ci-rt/testbox-shield/docs/r12.jpg

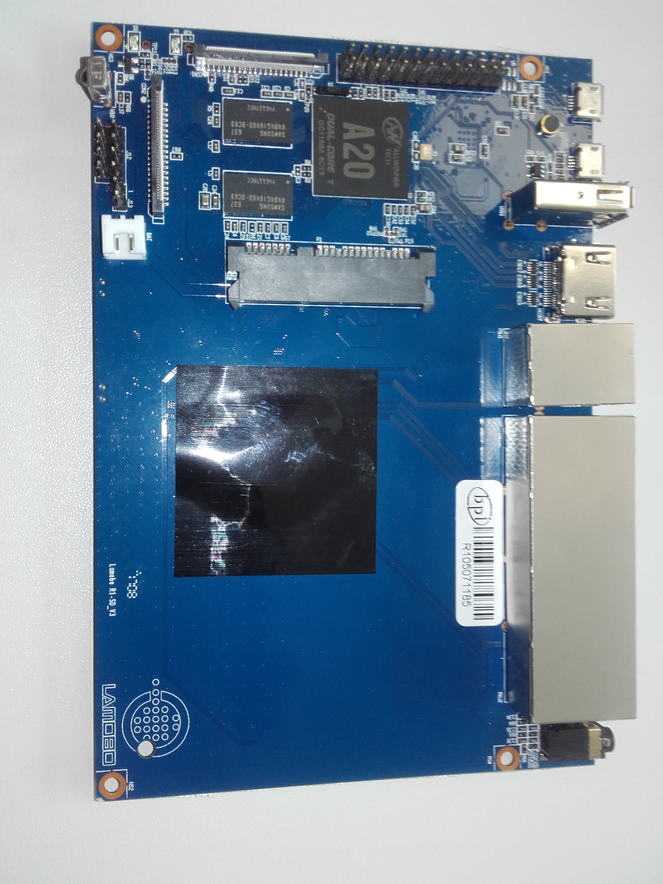
docs/r12.jpg
