ci-rt/testbox-shield/docs/Rocker_8600_8650_series-DTE.pdf

# 8600 Rocker Switches - Miniature

# 10A 250Vac Single & Double Pole

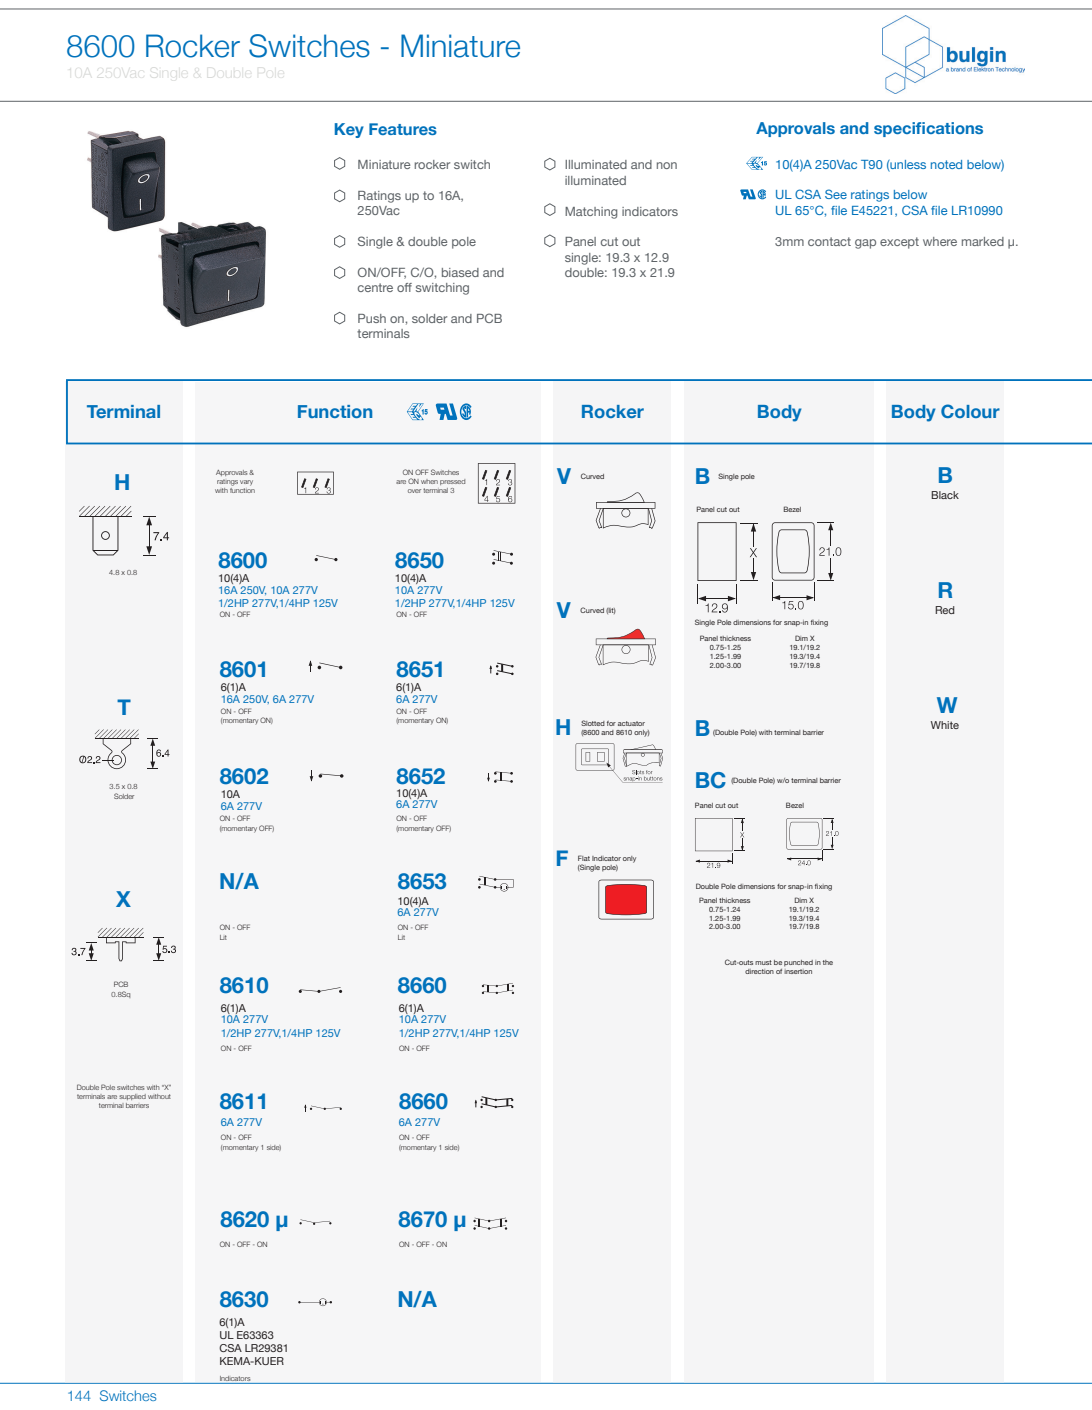
[picture p69: page 1]
144 Switches; Terminal; Function; 3.5 x 0.8 Solder; PCB 0.8Sq; Rocker; Body; Body Colour; V Curved; V Curved (lit); Indicators; 6(1)A UL E63363 CSA LR29381 KEMA-KUER; ON - OFF; (momentary ON); (momentary OFF); ON - OFF Lit; ON - OFF (momentary 1 side); ON - OFF - ON; Single pole; Panel cut out; Bezel; Dim X 19.1/19.2 19.3/19.4 19.7/19.8; Approvals & ratings vary with function; ON OFF Switches are ON when pressed over terminal 3; Key Features; Black; White; Red

Approvals and specifications

Miniature rocker switch
Ratings up to 16A,
250Vac
Single & double pole
ON/OFF, C/O, biased and
centre off switching
Push on, solder and PCB
terminals

Illuminated and non
illuminated
Matching indicators
Panel cut out
single: 19.3 x 12.9
double: 19.3 x 21.9

10(4)A 250Vac T90 (unless noted below)
UL CSA See ratings below
UL 65°C, file E45221, CSA file LR10990
3mm contact gap except where marked μ.

Single Pole dimensions for snap-in fixing
Panel thickness

Slotted for actuator H (8600 and 8610 only)

B(Double Pole) with terminal barrier

(Double Pole) w/o terminal barrier

Flat Indicator only F (Single pole)

Double Pole dimensions for snap-in fixing

Cut-outs must be punched in the
direction of insertion

Double Pole switches with “X”
terminals are supplied without
terminal barriers

# Dimensions

Single pole | Double pole

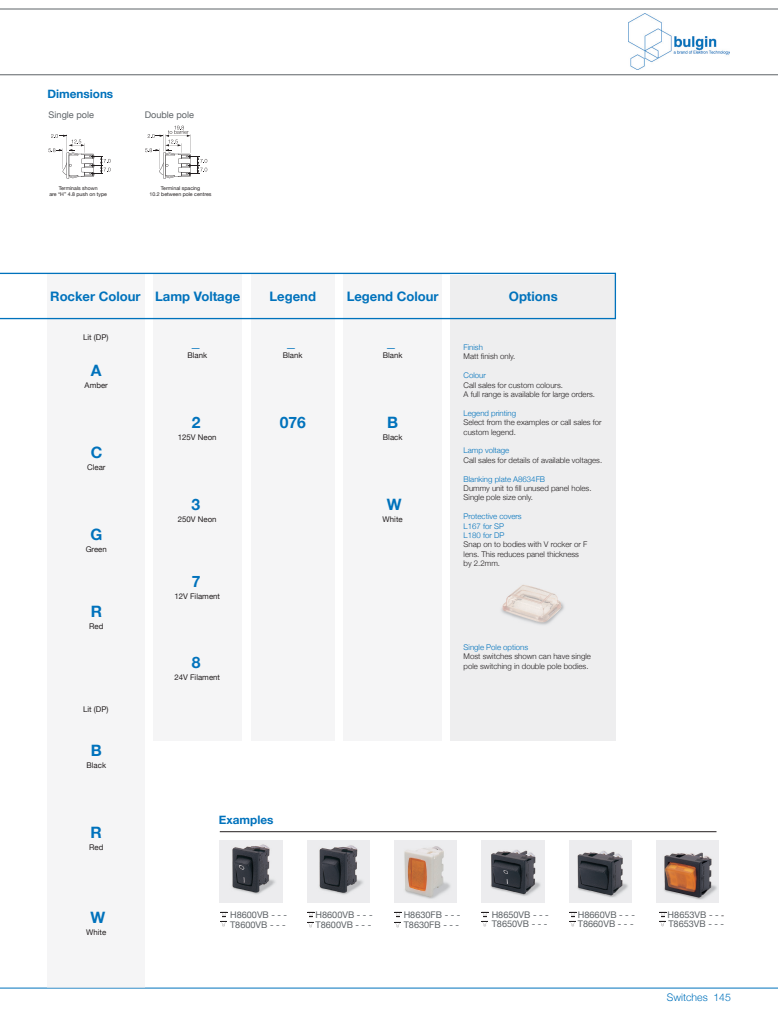
[picture p70: page 2]
Switches 145; Examples; Blank; Amber; Red; 12V Filament; 24V Filament; White; Green; 250V Neon; Black; Clear; 125V Neon; Lit (DP)

Terminals shown
are “H” 4.8 push on type

Terminal spacing
10.2 between pole centres

Rocker Colour | Lamp Voltage | Legend | Legend Colour | Options

Finish Matt finish only. Colour Call sales for custom colours. A full range is available for large orders. Legend printing Select from the examples or call sales for custom legend. Lamp voltage Call sales for details of available voltages. Blanking plate A8634FB Dummy unit to fill unused panel holes. Single pole size only. Protective covers L167 for SP L180 for DP Snap on to bodies with V rocker or F lens. This reduces panel thickness

Single Pole options
Most switches shown can have single
pole switching in double pole bodies.
