ci-rt/testbox-shield/docs/IRM-20-EN.pdf

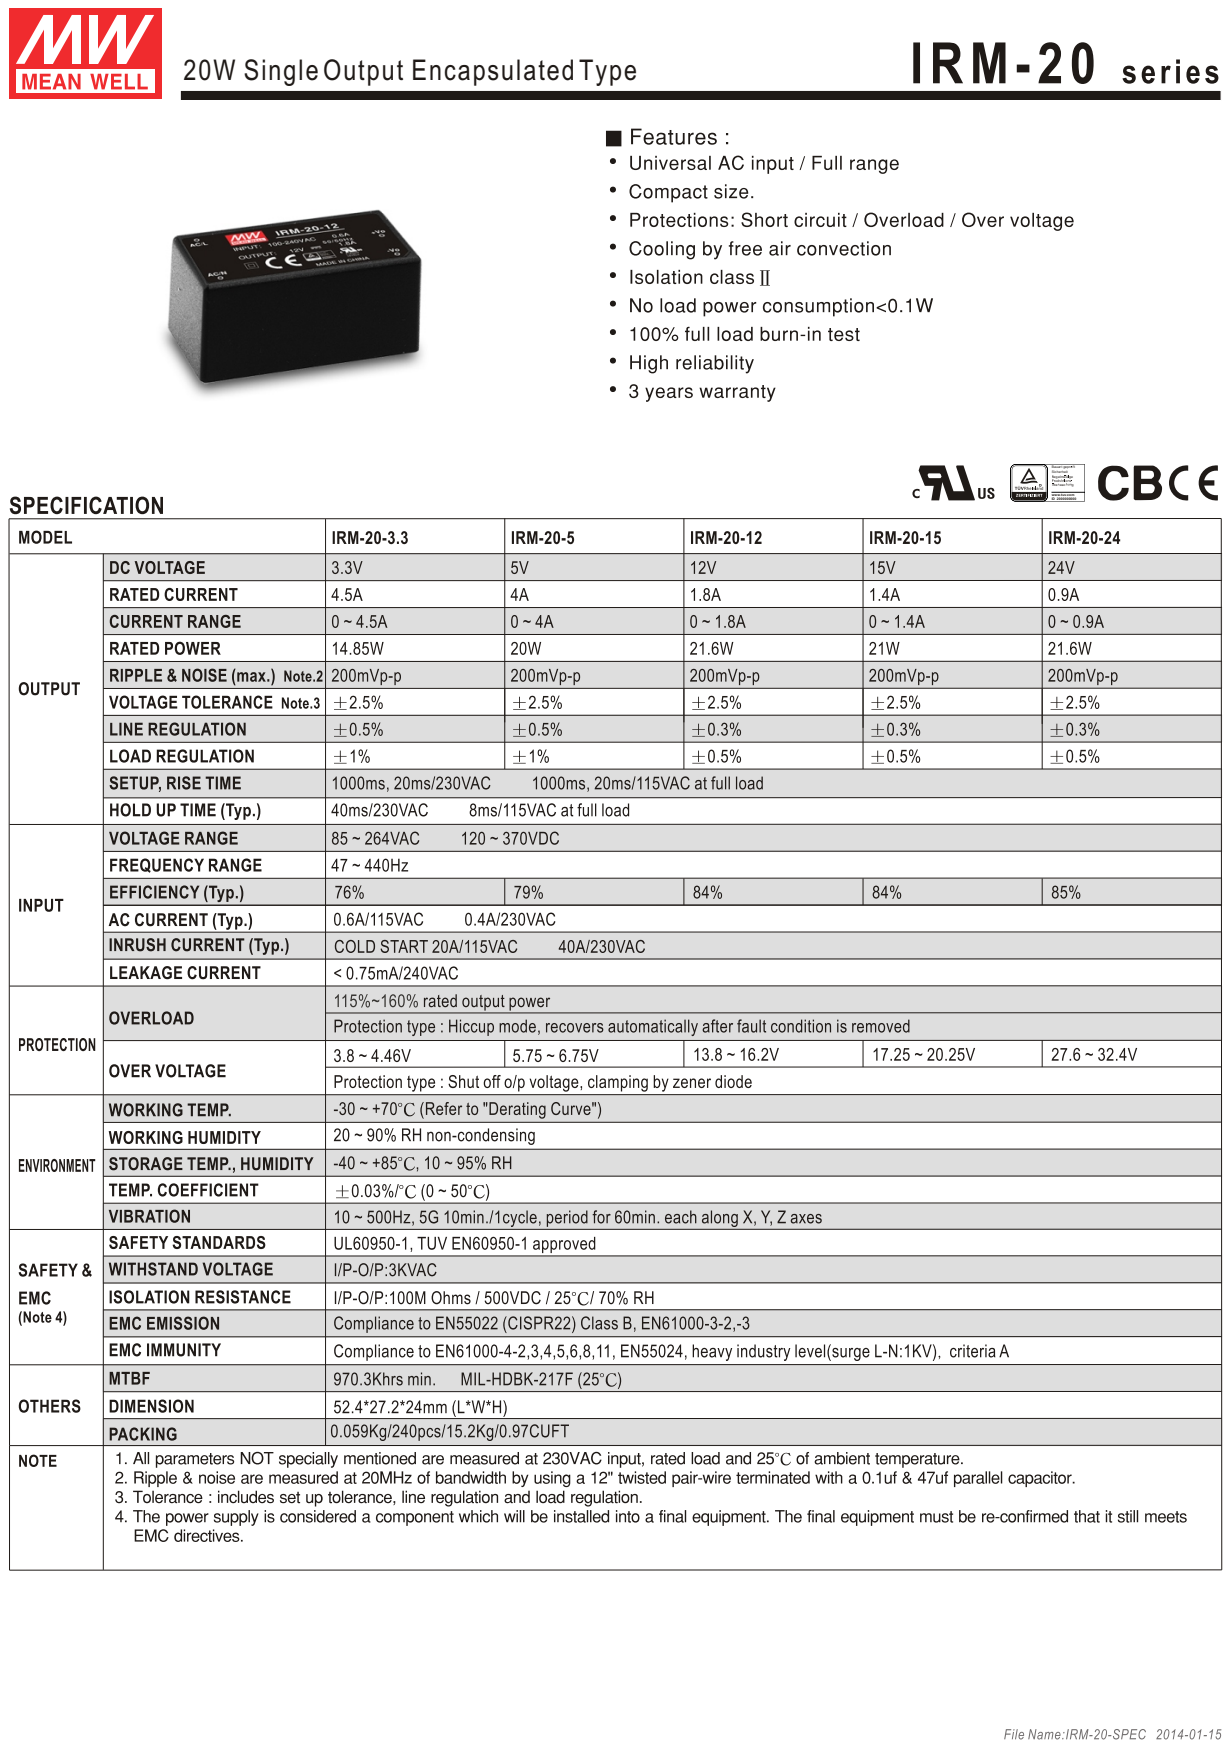
[picture p71: page 1]
Bauar Sicherheit egelma ge; t gepruft; www. ID 2000000000; tuv.com; wac

20W Single Output Encapsulated Type

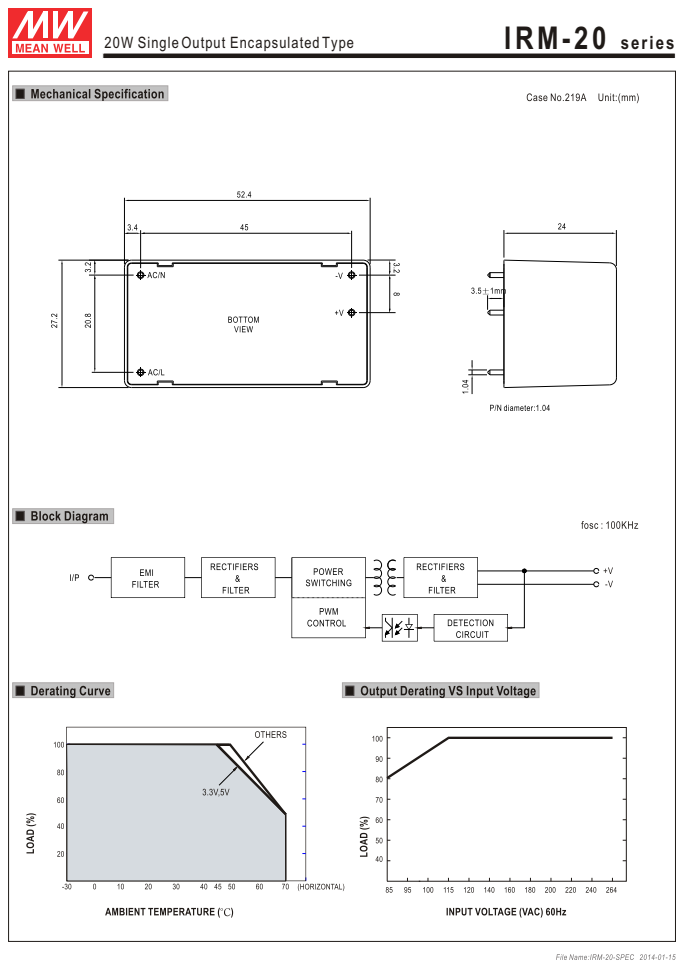
[picture p72: page 2]
20W Single Output Encapsulated Type; IRM-20 series
