ci-rt/testbox-shield/docs/TME-IEC-C-X.pdf

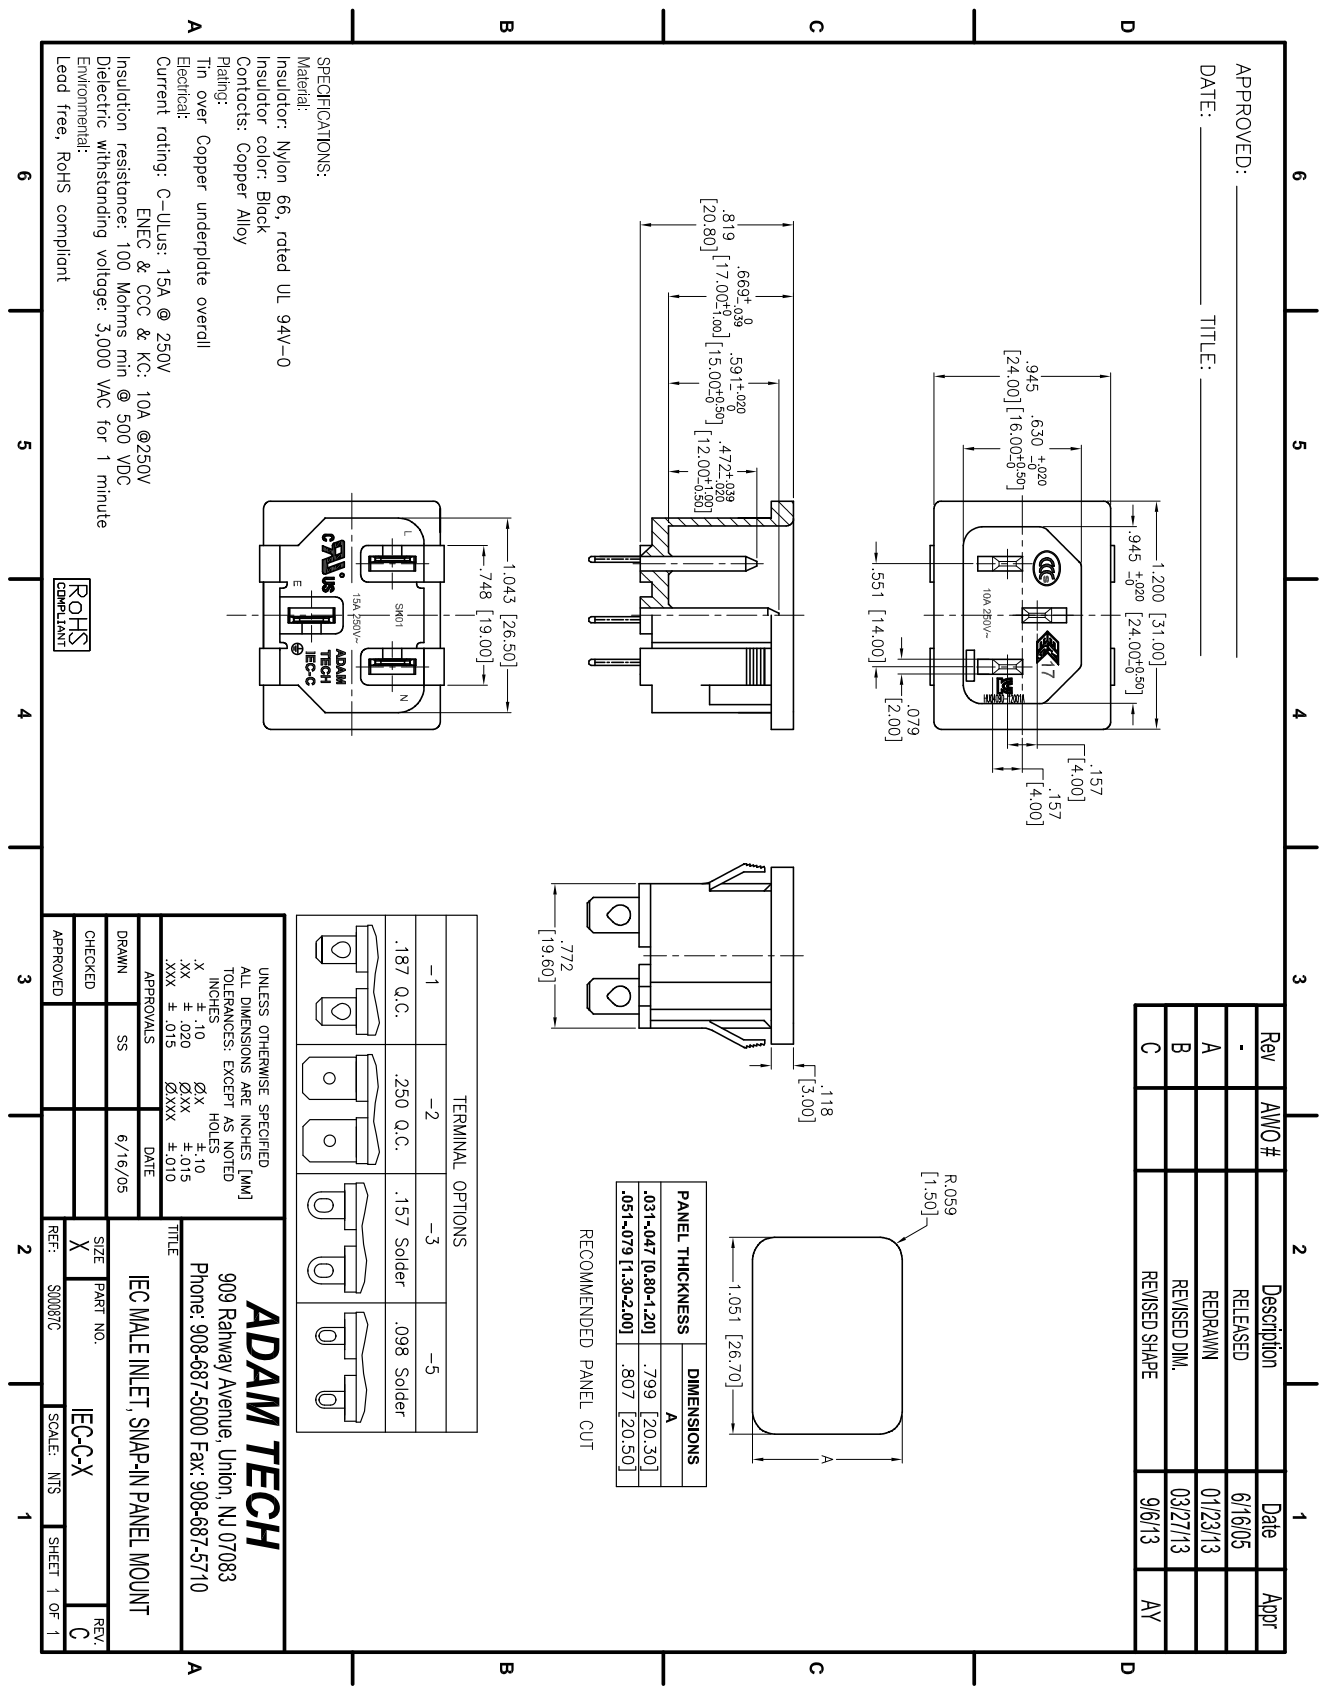
[picture p73: page 1]
