ci-rt/testbox-shield/docs/TME-IEC-D-X.pdf

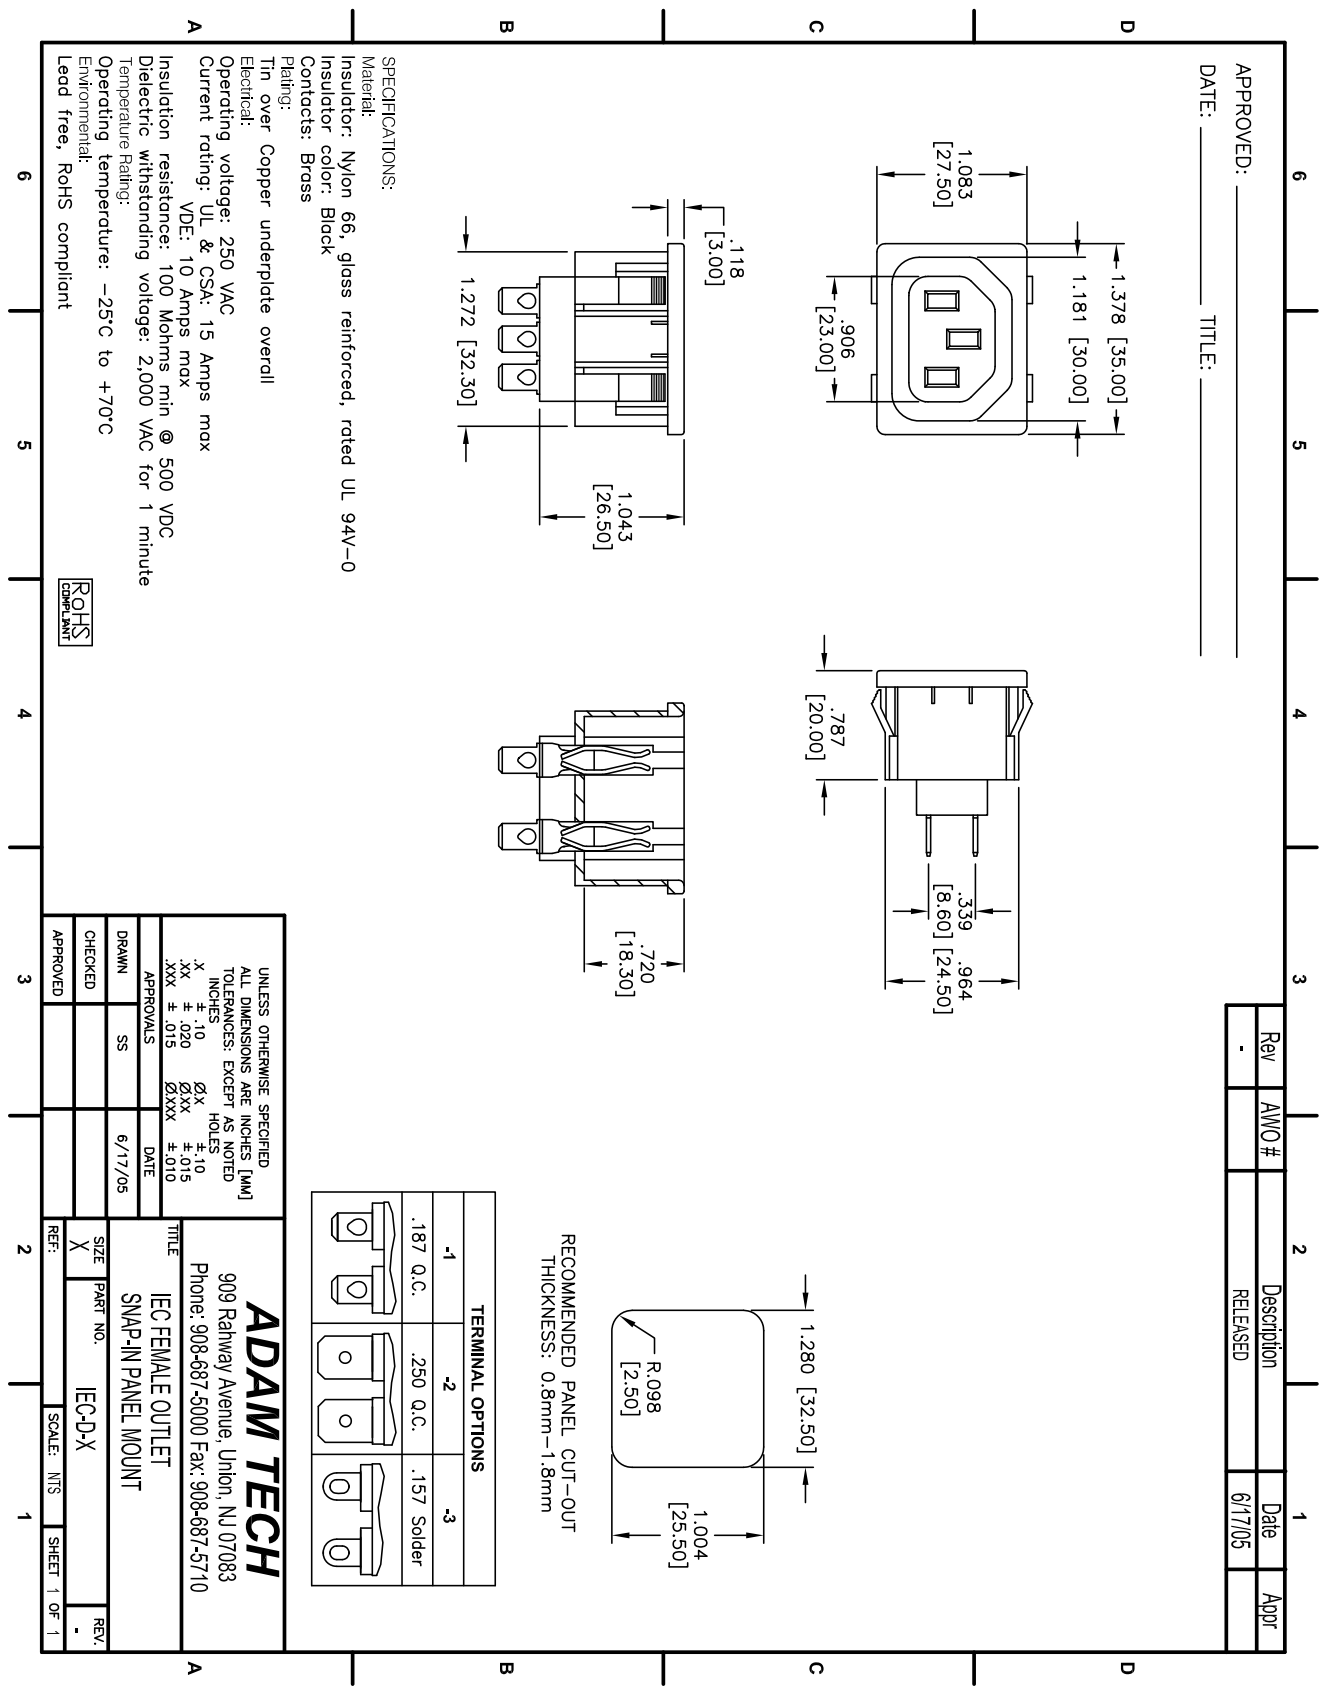
[picture p74: page 1]
