ci-rt/testbox-shield/docs/DS1034.pdf

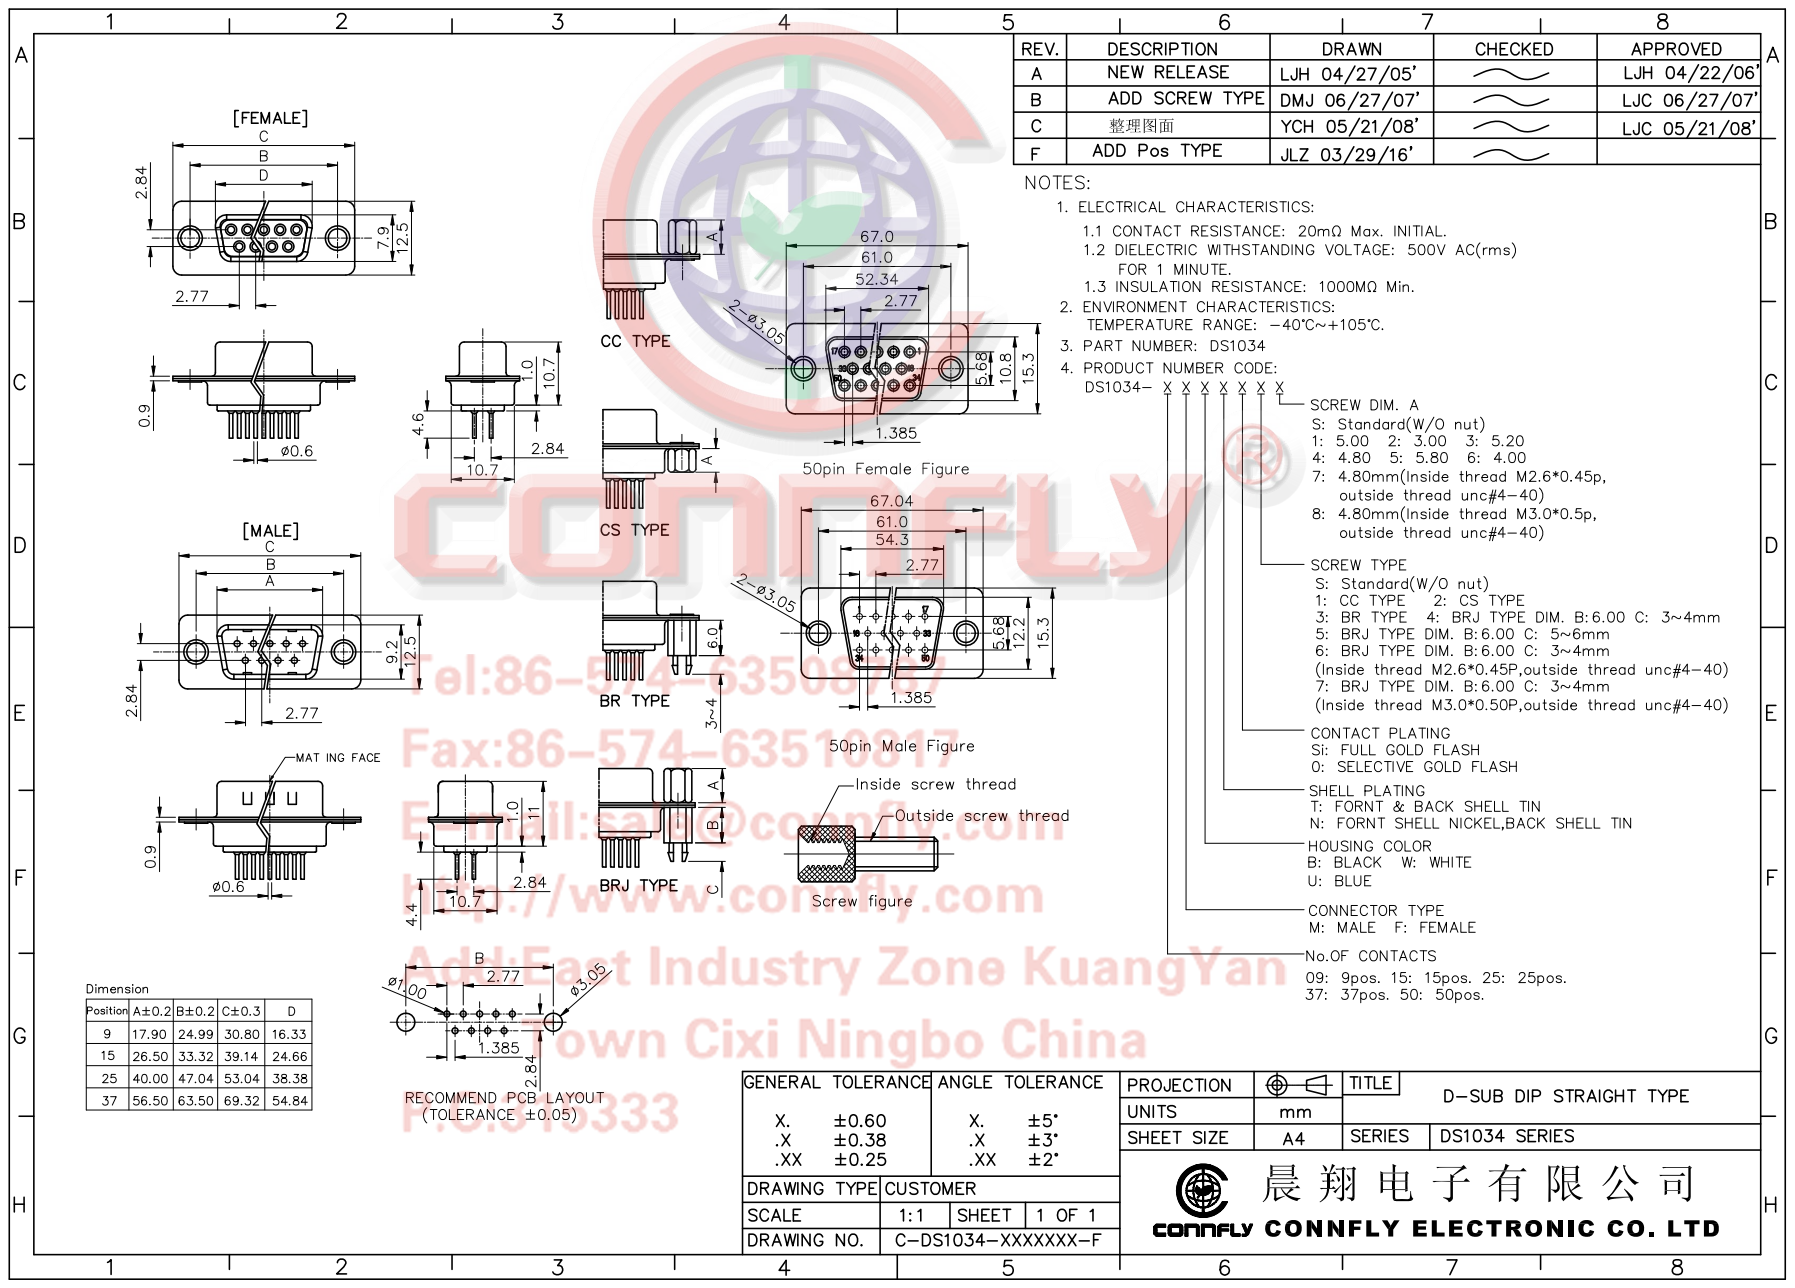
[picture p75: page 1]
